libu2548/cr10core/CAD/toolhead/v1.png

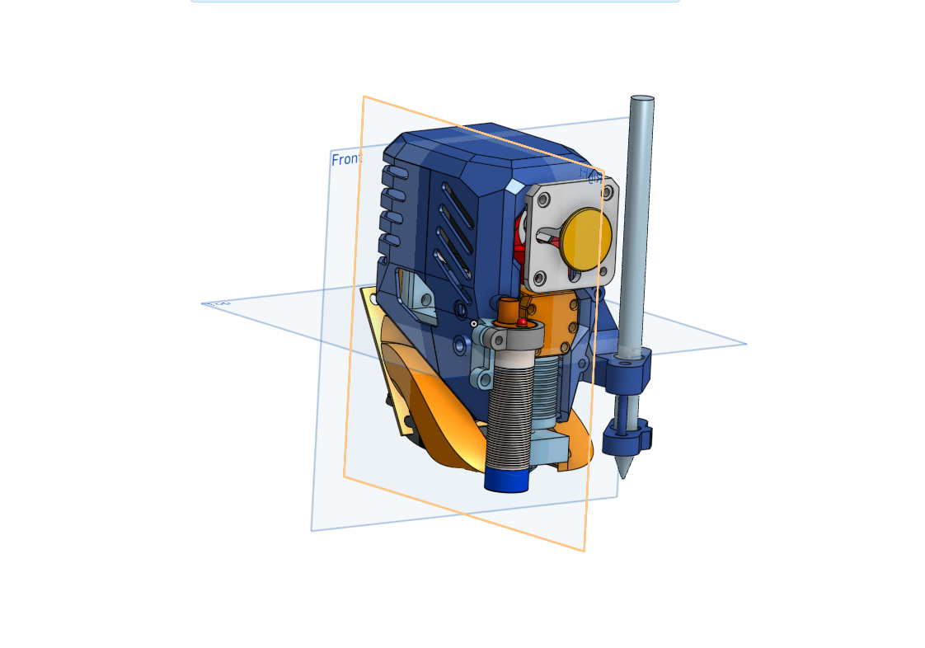
CAD/toolhead/v1.png
