libu2548/cr10core/CAD/toolhead/v3.png

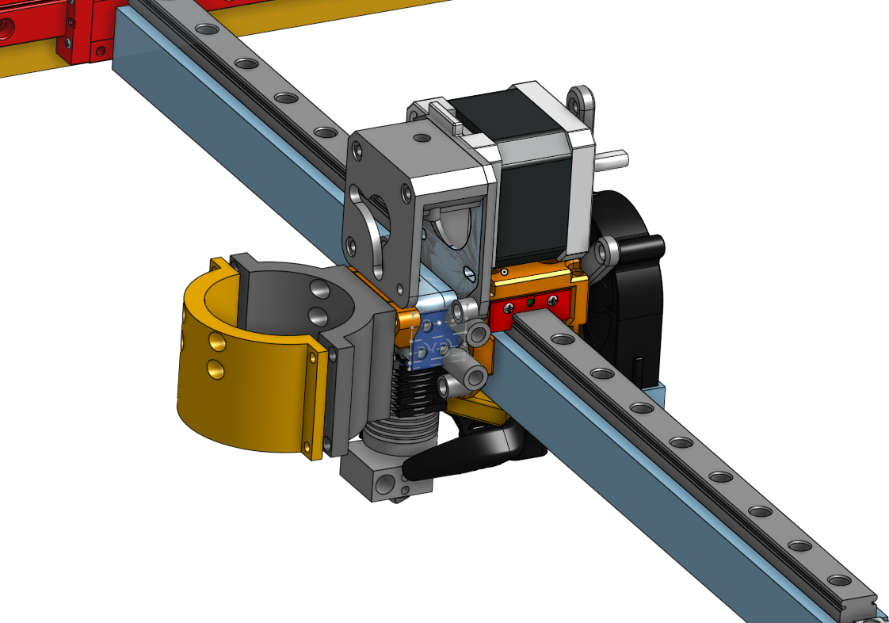
CAD/toolhead/v3.png
