libu2548/cr10core/CAD/toolhead/v4.png

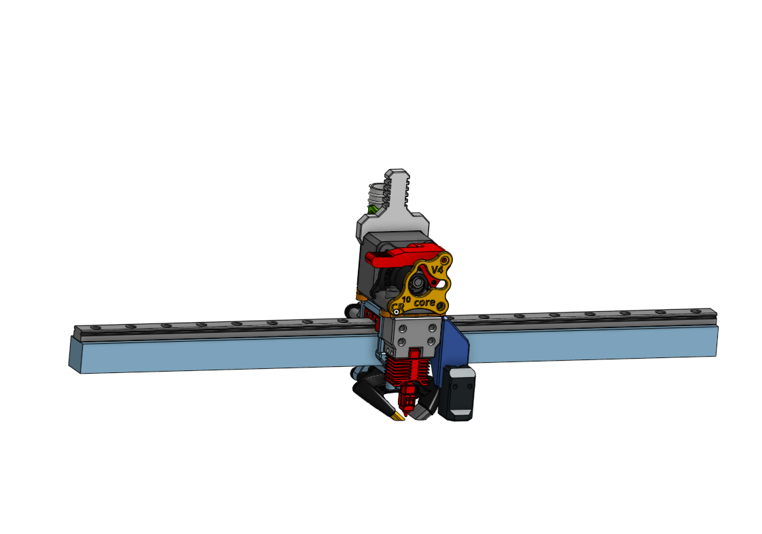
CAD/toolhead/v4.png
