libu2548/cr10core/CAD/toolhead/V5.png

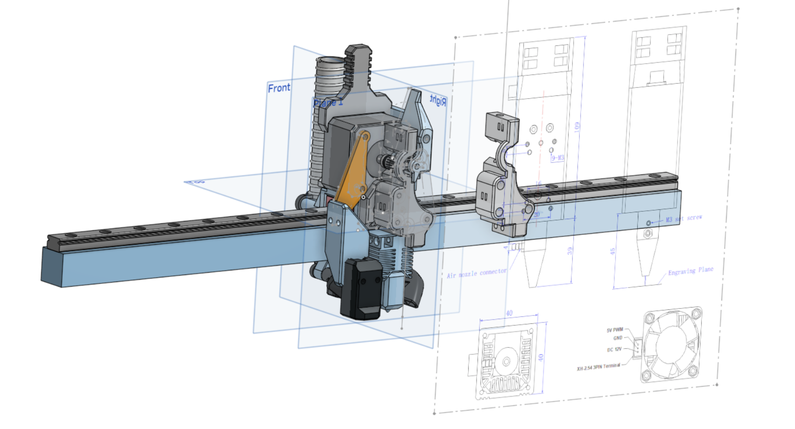
CAD/toolhead/V5.png
