libu2548/cr10core/image/20260116_104110.jpg

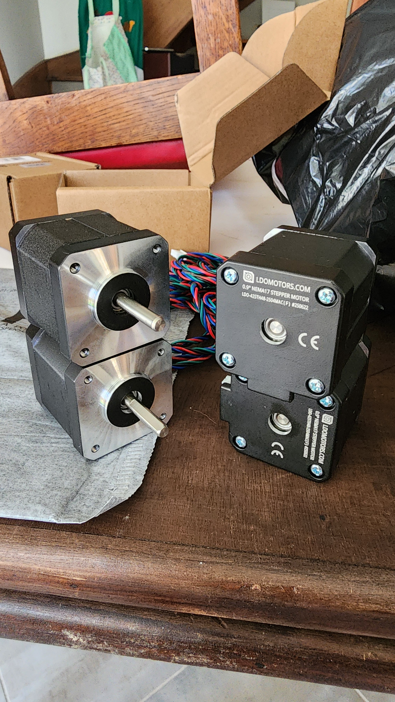
image/20260116_104110.jpg
