libu2548/cr10core/image/20260117_215310.jpg

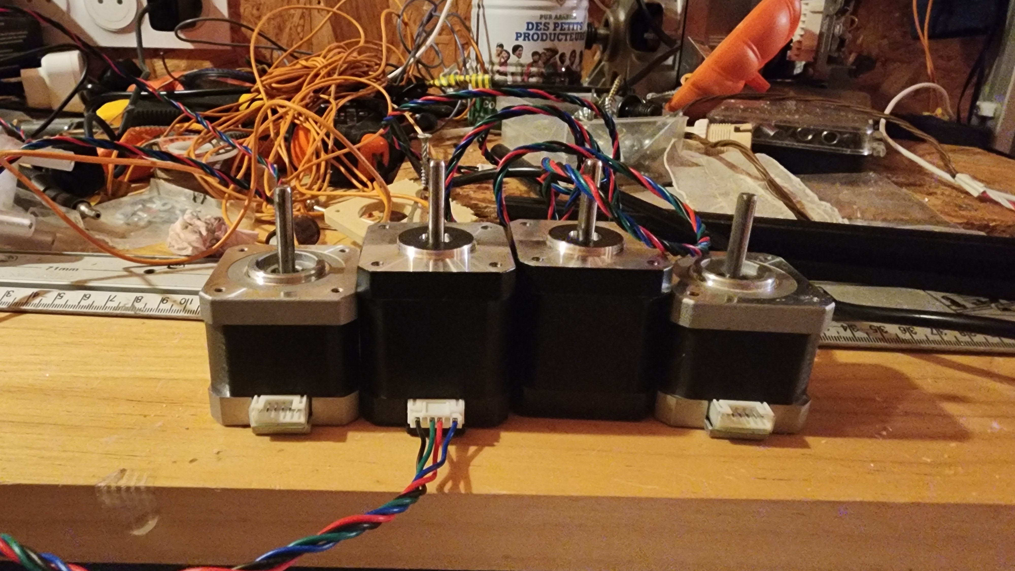
image/20260117_215310.jpg
