libu2548/cr10core/image/20260119_152943.jpg

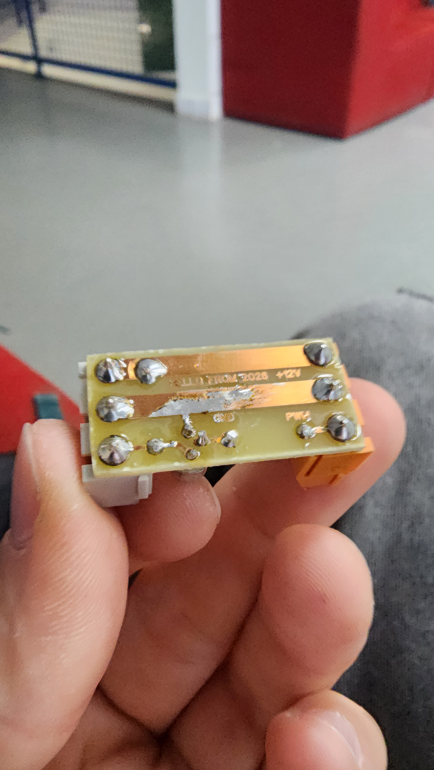
image/20260119_152943.jpg
