libu2548/cr10core/image/20260119_152947.jpg

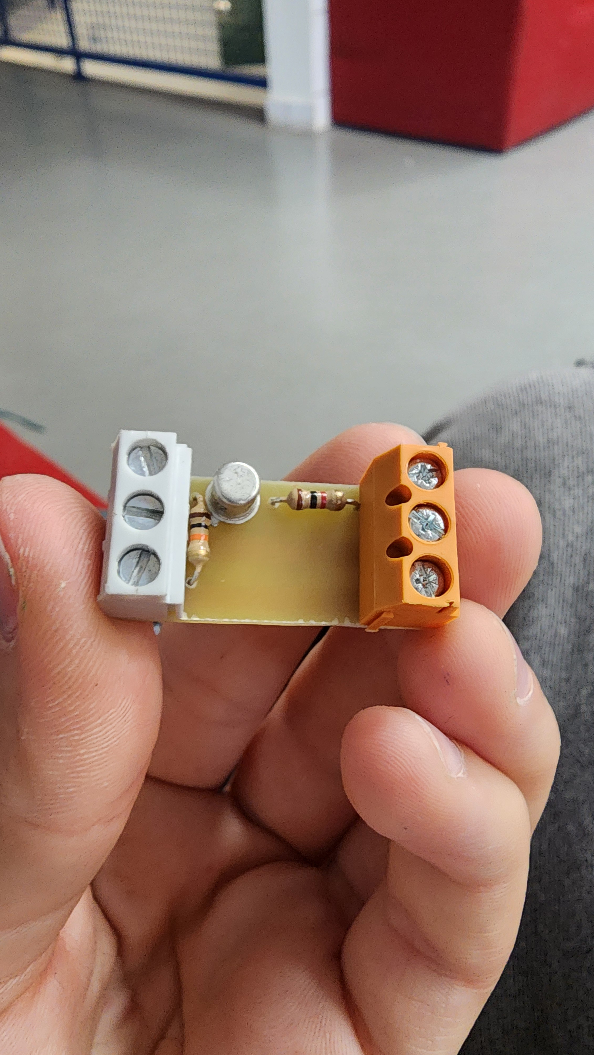
image/20260119_152947.jpg
