libu2548/cr10core/image/20260124_153731.jpg

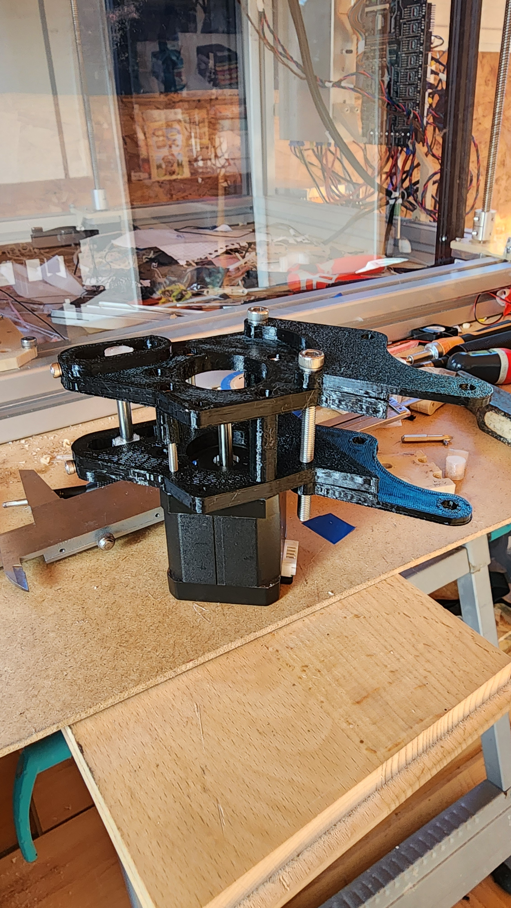
image/20260124_153731.jpg
