libu2548/cr10core/image/20260127_170606.jpg

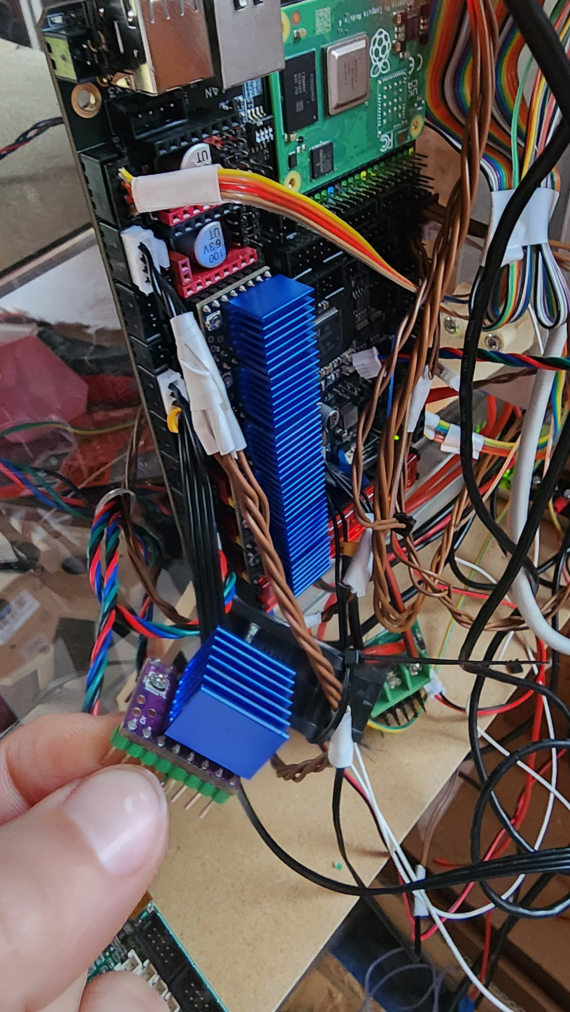
image/20260127_170606.jpg
