libu2548/cr10core/image/20260131_212745.jpg

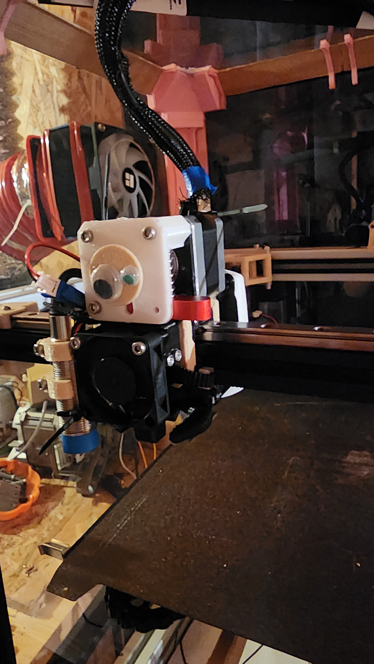
image/20260131_212745.jpg
