libu2548/cr10core/image/20260507_145341.jpg

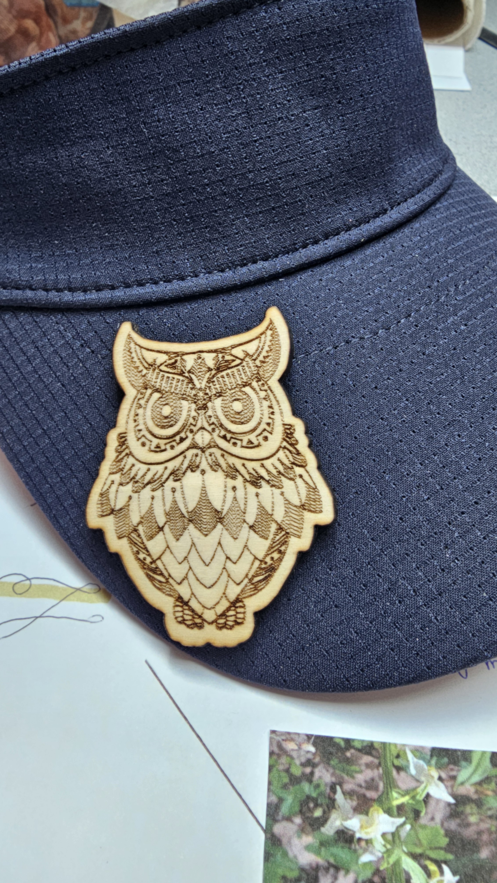
image/20260507_145341.jpg
