libu2548/cr10core/image/20260507_165830.jpg

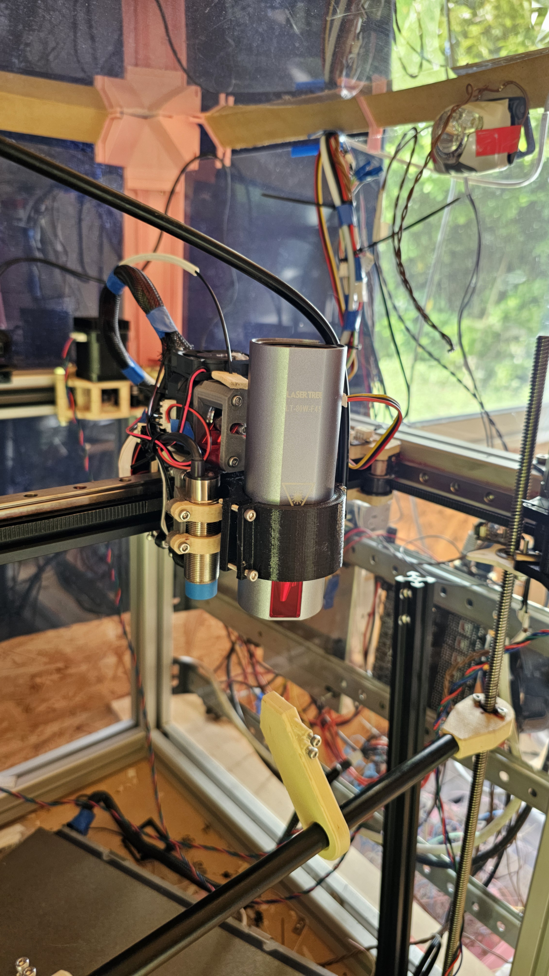
image/20260507_165830.jpg
