libu2548/cr10core/image/20260508_215619.jpg

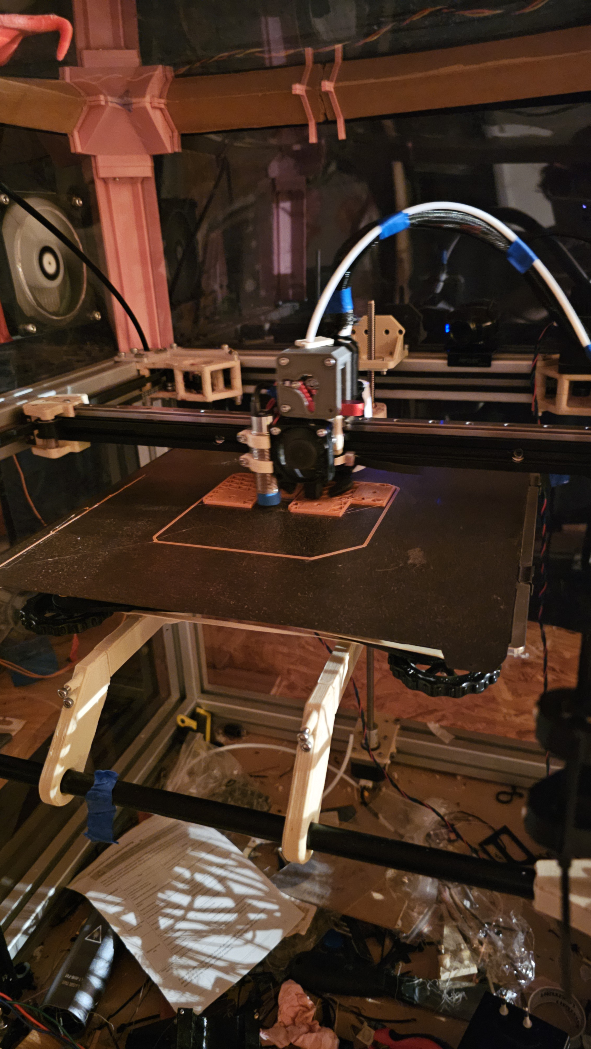
image/20260508_215619.jpg
