libu2548/cr10core/image/20260521_215504.jpg

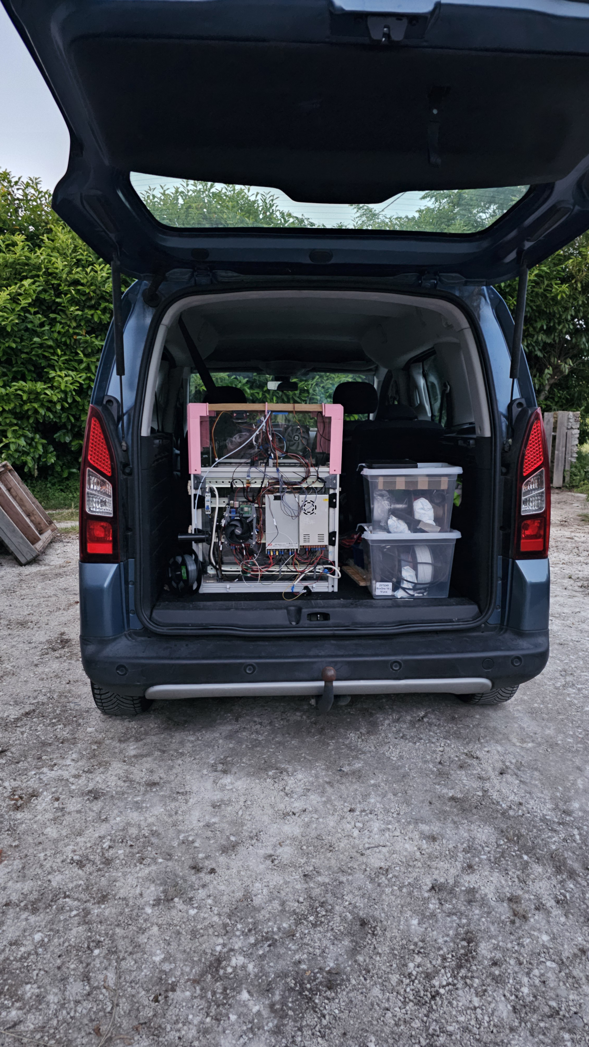
image/20260521_215504.jpg
