libu2548/cr10core/image/20260522_083416.jpg

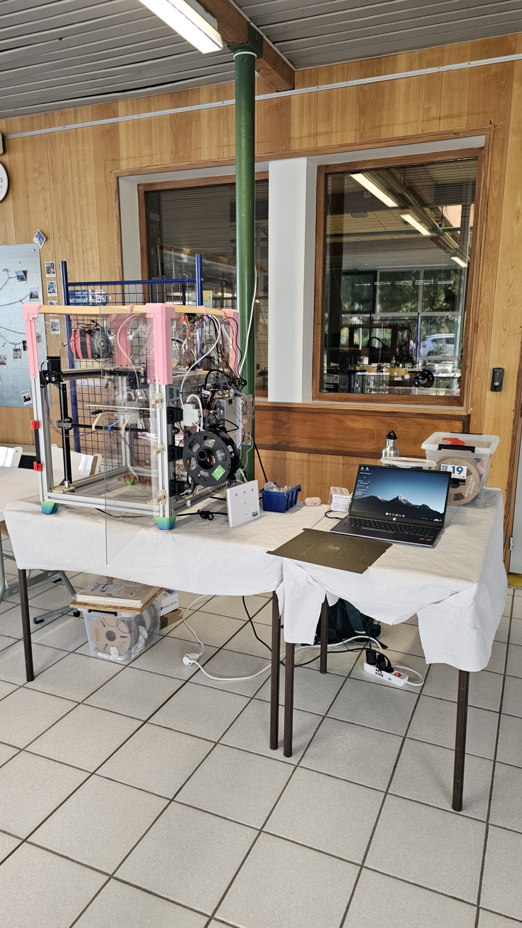
image/20260522_083416.jpg
