libu2548/cr10core/image/20260602_214717.jpg

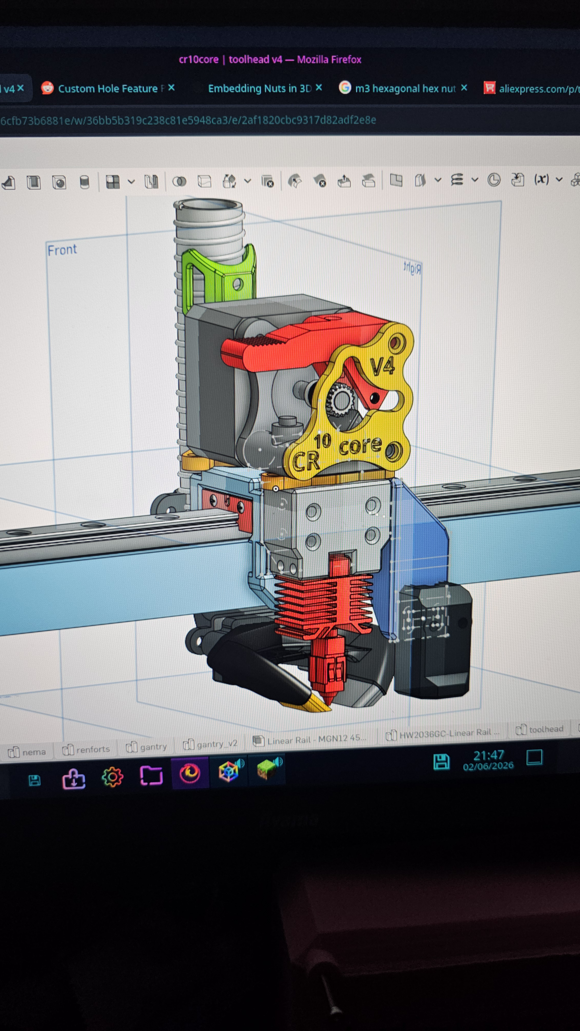
image/20260602_214717.jpg
