libu2548/cr10core/image/20260611_225606.jpg

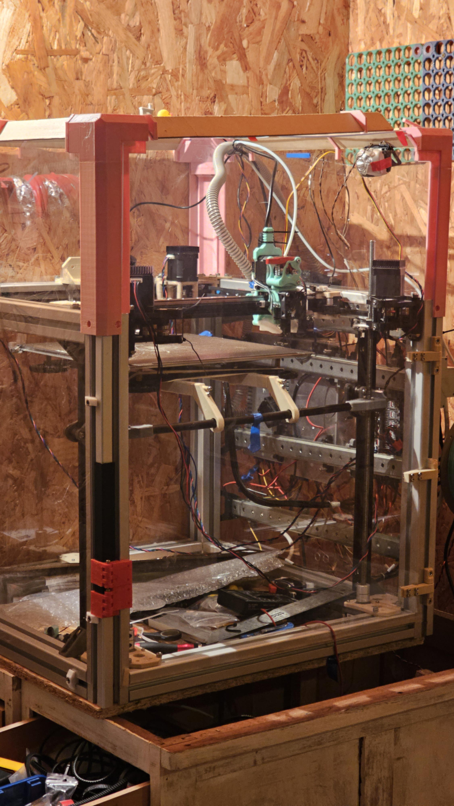
image/20260611_225606.jpg
