libu2548/cr10core/image/20260623_185925.jpg

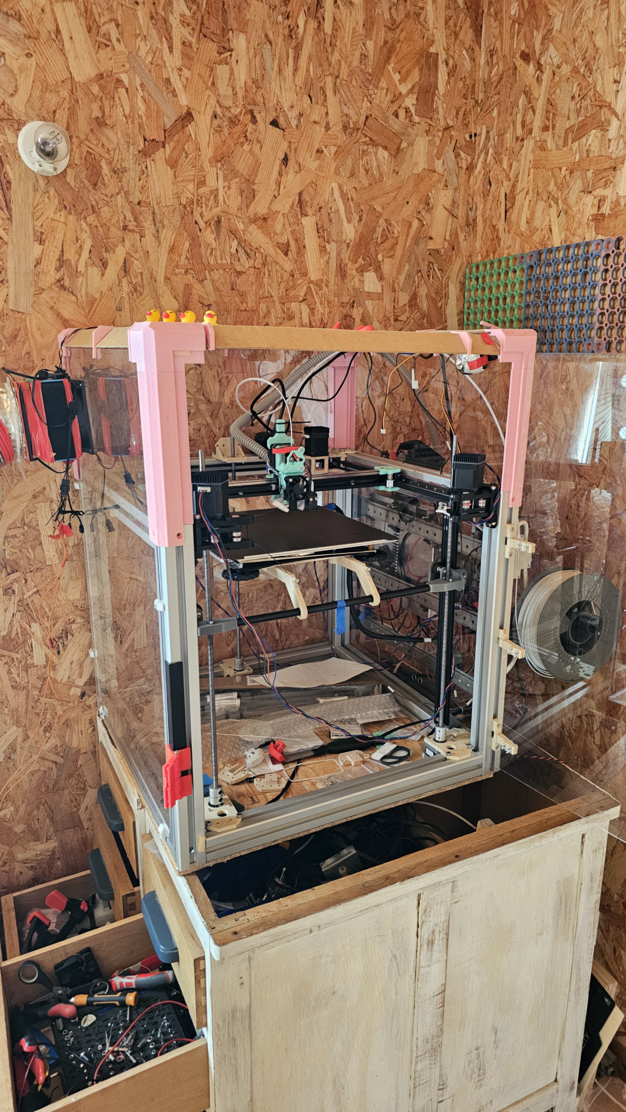
image/20260623_185925.jpg
