libu2548/cr10core/image/20260626_155403.jpg

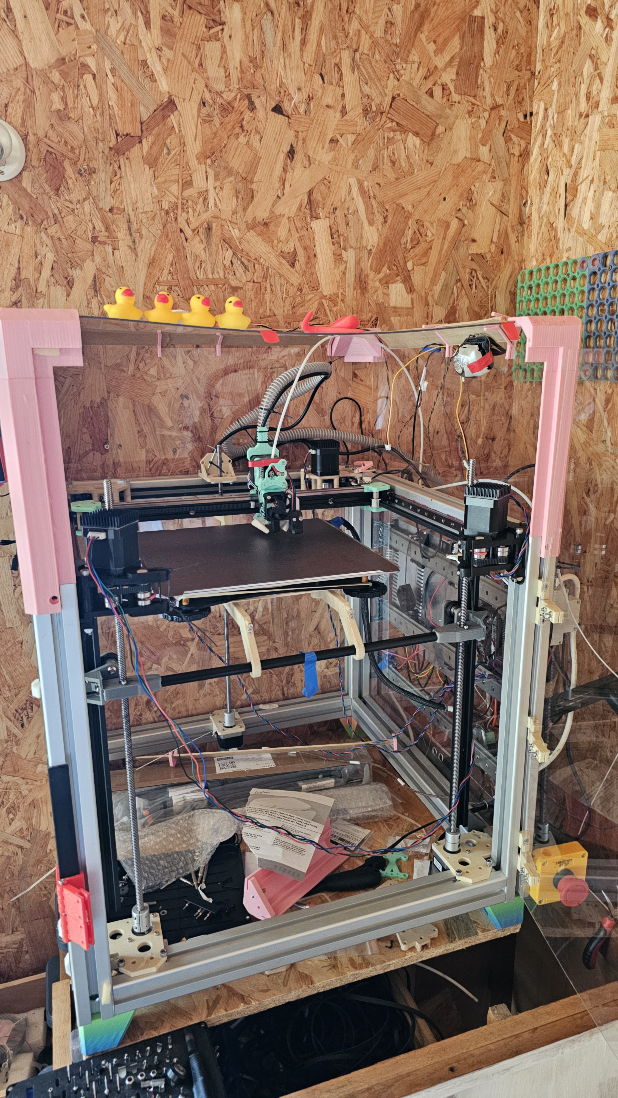
image/20260626_155403.jpg
