libu2548/cr10core/image/20260629_121632.jpg

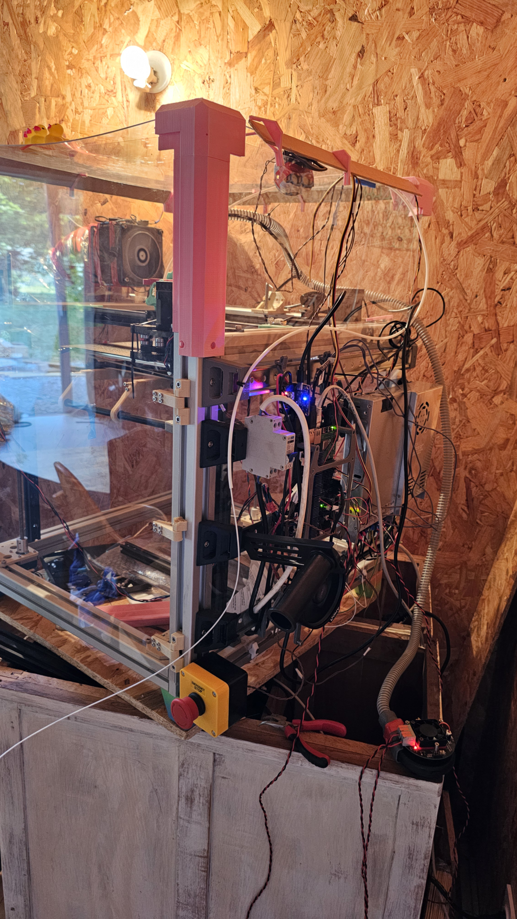
image/20260629_121632.jpg
