libu2548/cr10core/image/20260630_170940.jpg

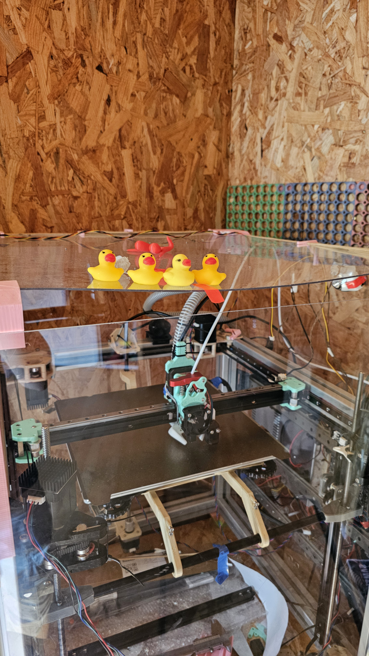
image/20260630_170940.jpg
