libu2548/cr10core/image/20260810_182935.jpg

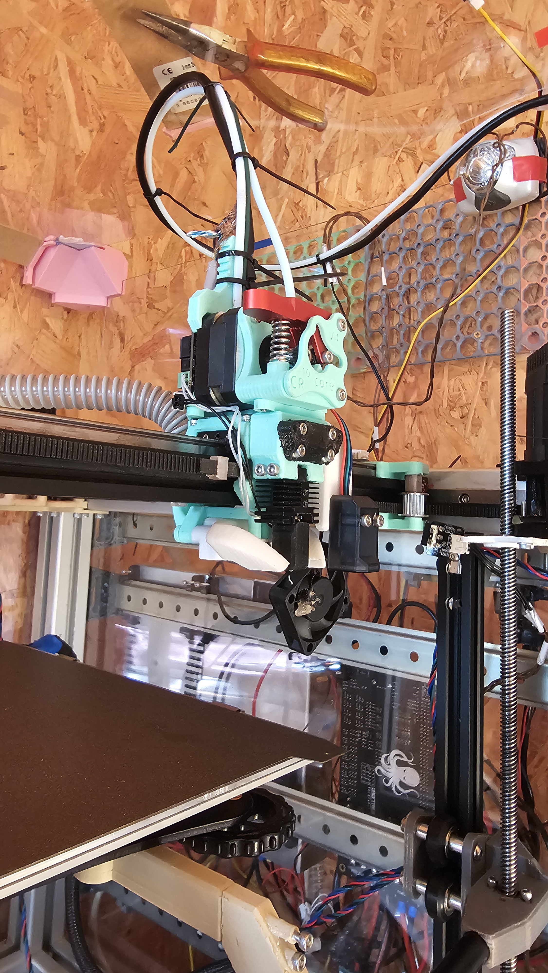
image/20260810_182935.jpg
