libu2548/cr10core/image/20260810_183454.jpg

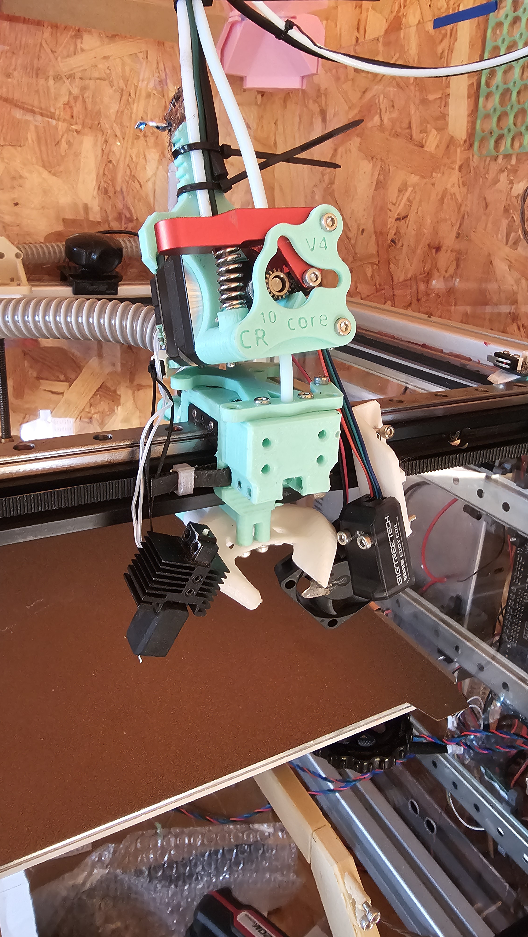
image/20260810_183454.jpg
