libu2548/cr10core/image/20260810_183547.jpg

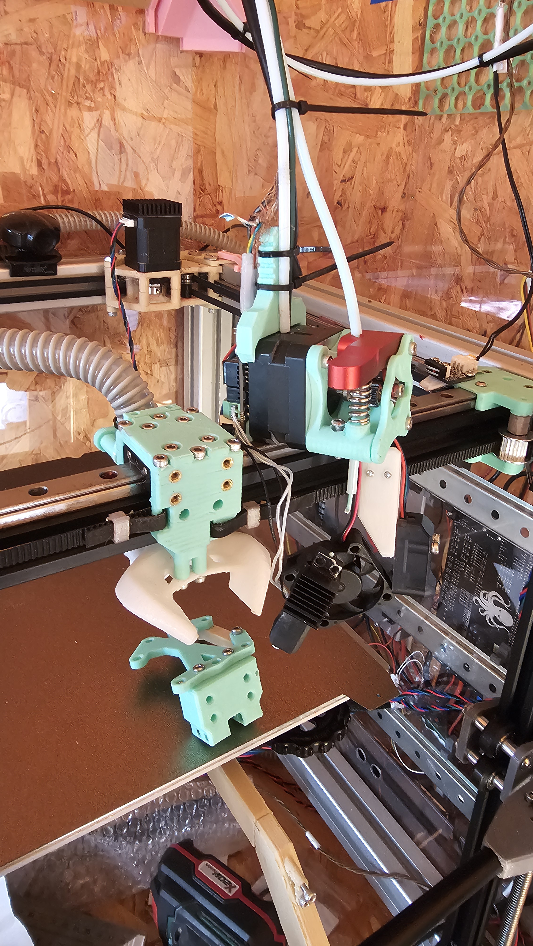
image/20260810_183547.jpg
