libu2548/cr10core/image/20260810_230010.jpg

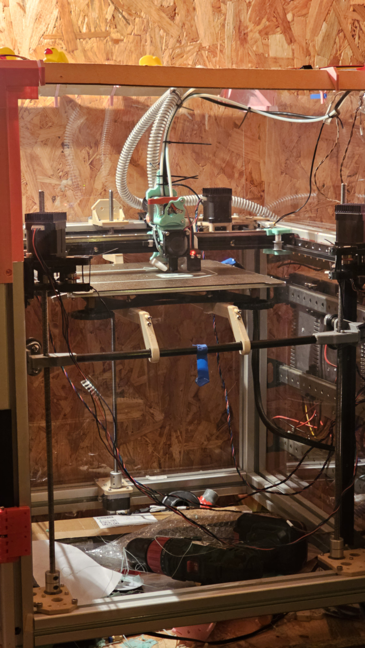
image/20260810_230010.jpg
