libu2548/cr10core/image/20260913_220324.jpg

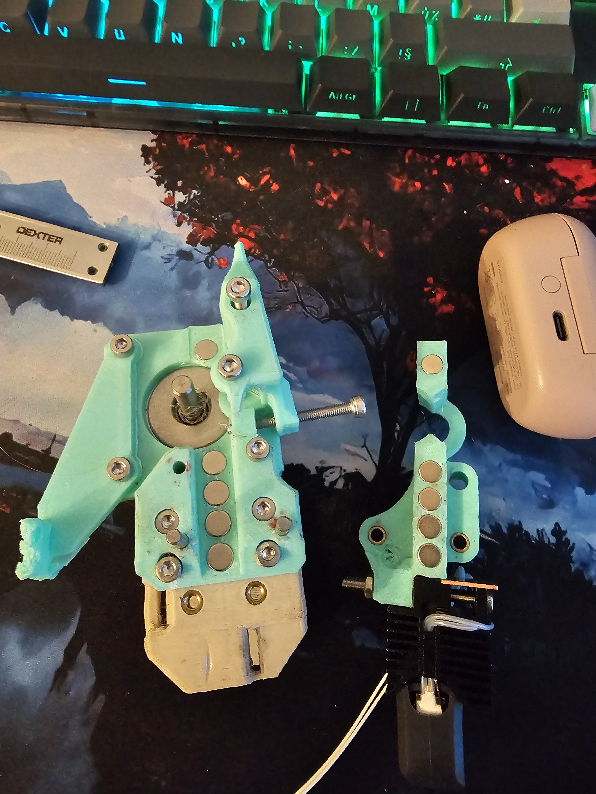
image/20260913_220324.jpg
