libu2548/cr10core/CAD/toolhead/toolhead v4 indiv files/toolhead v4 - Open CASCADE STEP translator 6.8 1.1.1.step

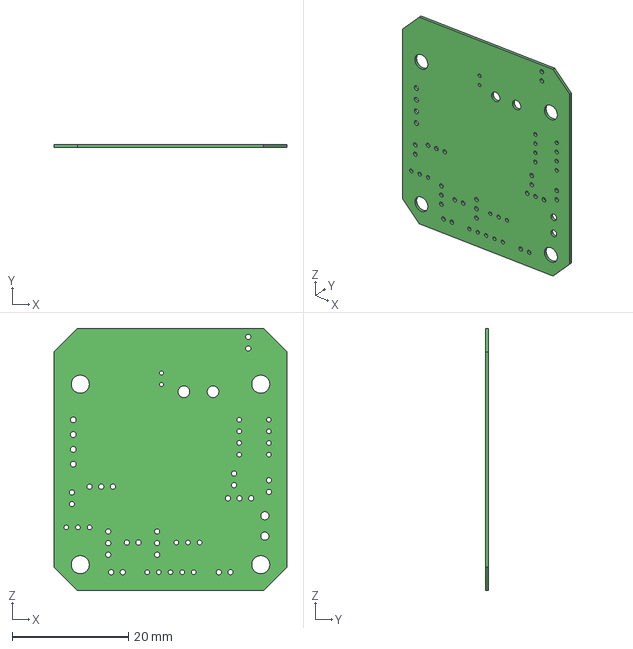
[picture p53: CAD file, 2026-08-19]
CAD/toolhead/toolhead v4 indiv files/toolhead v4 - Open CASCADE STEP translator 6.8 1.1.1.step
40.0 x 0.558 x 45.0 mm
