libu2548/cr10core/CAD/toolhead/toolhead v4 indiv files/toolhead v4 - MGN12C Carriage v1.step

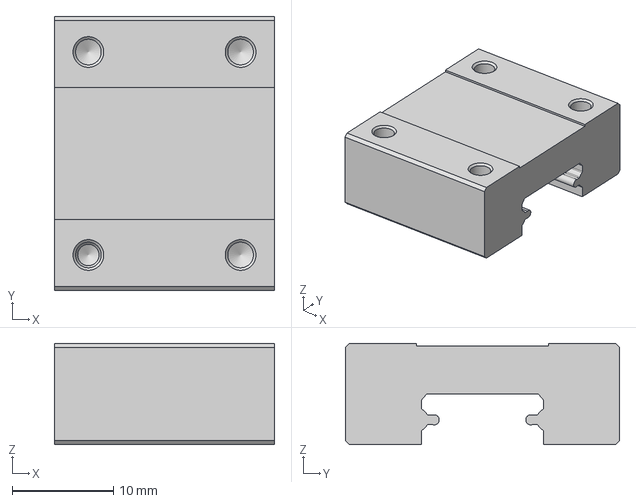
[picture p54: CAD file, 2026-08-19]
CAD/toolhead/toolhead v4 indiv files/toolhead v4 - MGN12C Carriage v1.step
21.7 x 27.0 x 10.0 mm
