libu2548/cr10core/CAD/toolhead/toolhead v4 indiv files/toolhead v4 - Part 22.step

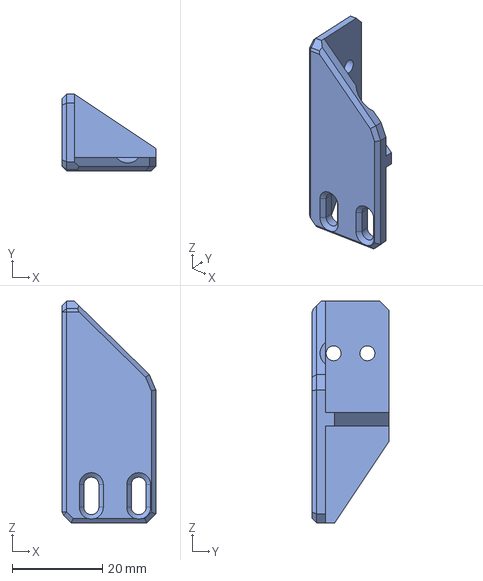
[picture p55: CAD file, 2026-08-19]
CAD/toolhead/toolhead v4 indiv files/toolhead v4 - Part 22.step
20.8 x 17.0 x 49.2 mm
