libu2548/cr10core/CAD/toolhead/toolhead v4 indiv files/toolhead v4 - CPAP clamp.step

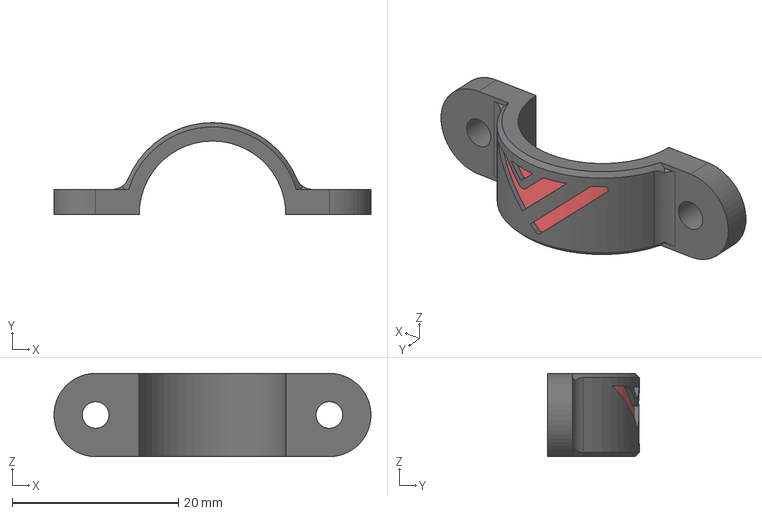
[picture p56: CAD file, 2026-08-19]
CAD/toolhead/toolhead v4 indiv files/toolhead v4 - CPAP clamp.step
38.1 x 11.0 x 10.0 mm
