libu2548/cr10core/CAD/toolhead/toolhead v4 indiv files/toolhead v4 - Motor gear.step

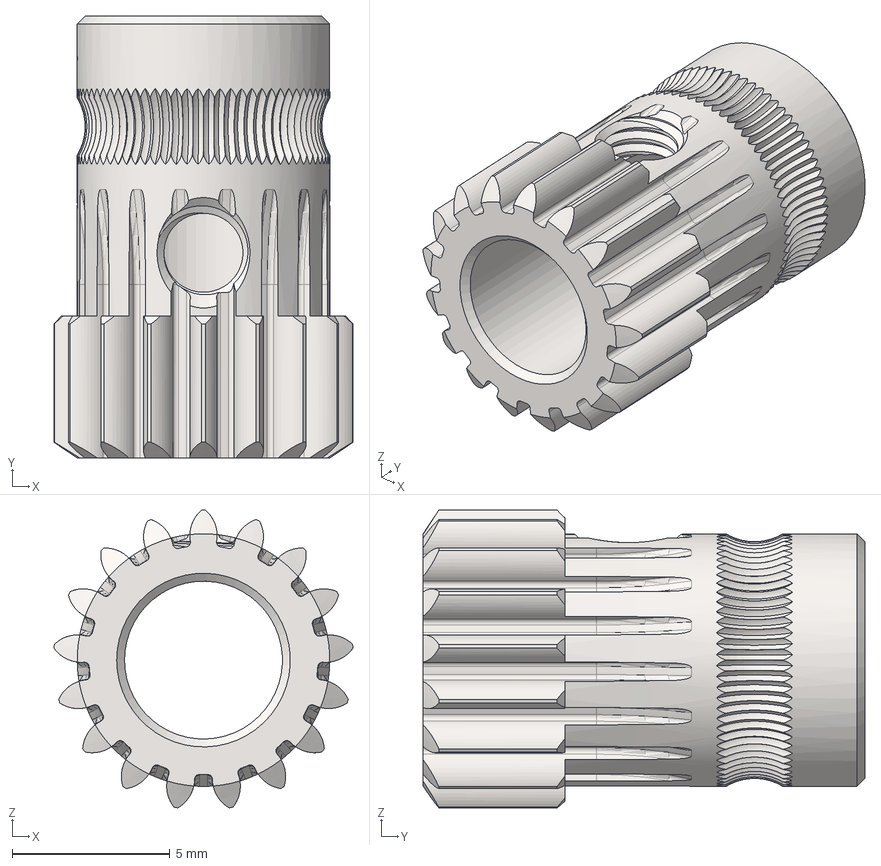
[picture p57: CAD file, 2026-08-19]
CAD/toolhead/toolhead v4 indiv files/toolhead v4 - Motor gear.step
9.47 x 14.0 x 9.43 mm
