libu2548/cr10core/CAD/toolhead/toolhead v4 indiv files/toolhead v4 - Part 31.step

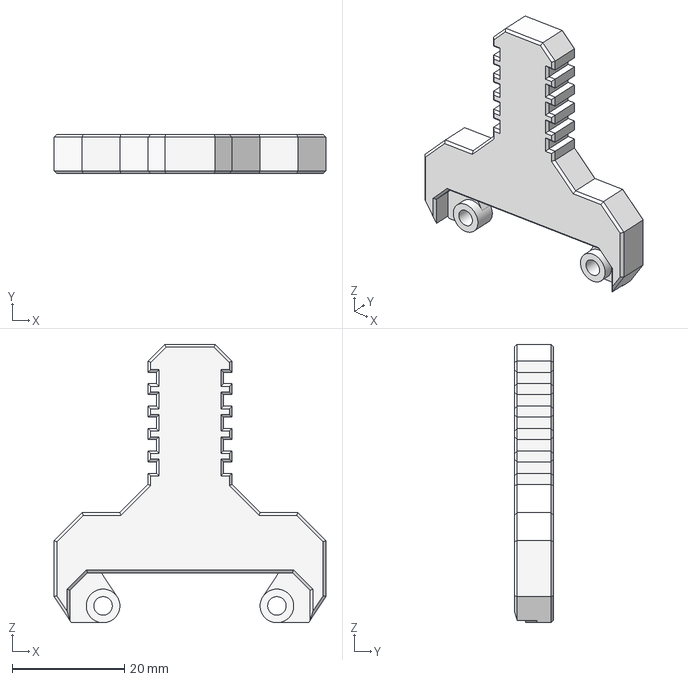
[picture p58: CAD file, 2026-08-19]
CAD/toolhead/toolhead v4 indiv files/toolhead v4 - Part 31.step
48.5 x 7.00 x 49.6 mm
