libu2548/cr10core/CAD/toolhead/toolhead v4 indiv files/toolhead v4 - chassis.step

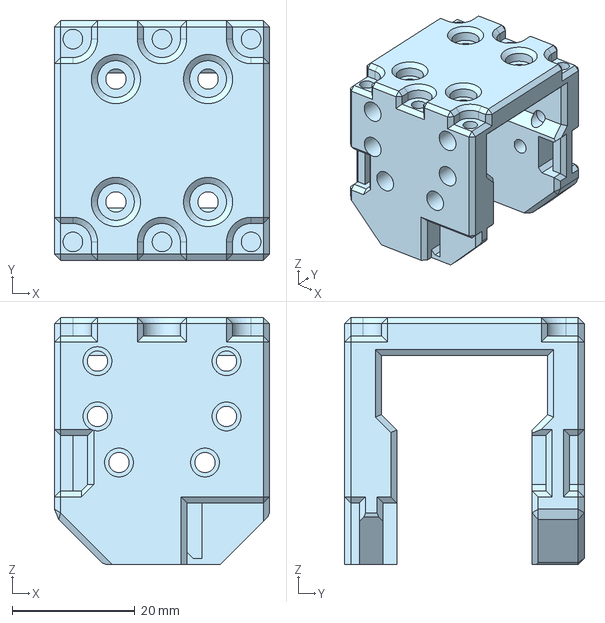
[picture p59: CAD file, 2026-08-19]
CAD/toolhead/toolhead v4 indiv files/toolhead v4 - chassis.step
35.0 x 39.0 x 40.2 mm
