libu2548/cr10core/CAD/toolhead/toolhead v4 indiv files/toolhead v4 - extrudeur.step

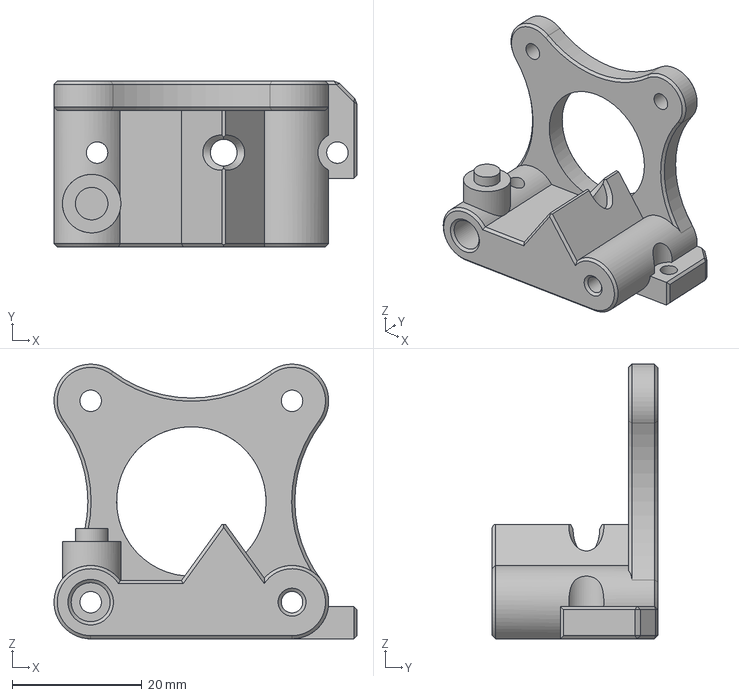
[picture p60: CAD file, 2026-08-19]
CAD/toolhead/toolhead v4 indiv files/toolhead v4 - extrudeur.step
46.6 x 25.5 x 42.3 mm
