libu2548/cr10core/CAD/toolhead/toolhead v4 indiv files/toolhead v4 - cable holder Vz (1).step

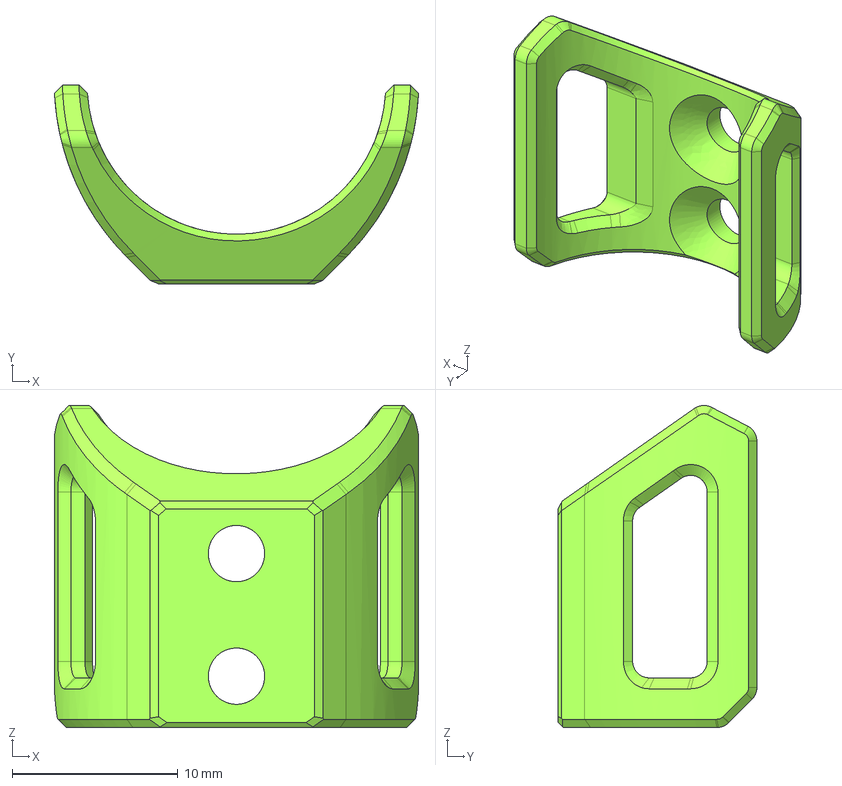
[picture p61: CAD file, 2026-08-19]
CAD/toolhead/toolhead v4 indiv files/toolhead v4 - cable holder Vz (1).step
22.0 x 12.0 x 19.4 mm
