libu2548/cr10core/CAD/toolhead/toolhead v4 indiv files/toolhead v4 - Part 29.step

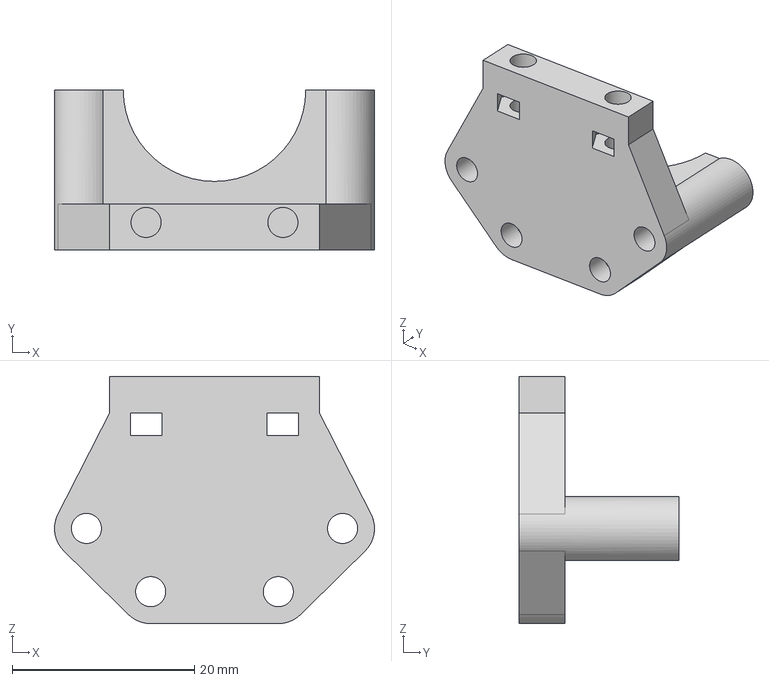
[picture p62: CAD file, 2026-08-19]
CAD/toolhead/toolhead v4 indiv files/toolhead v4 - Part 29.step
35.1 x 17.5 x 27.1 mm
