libu2548/cr10core/CAD/toolhead/toolhead v4 indiv files/toolhead v4 - Hotend.step

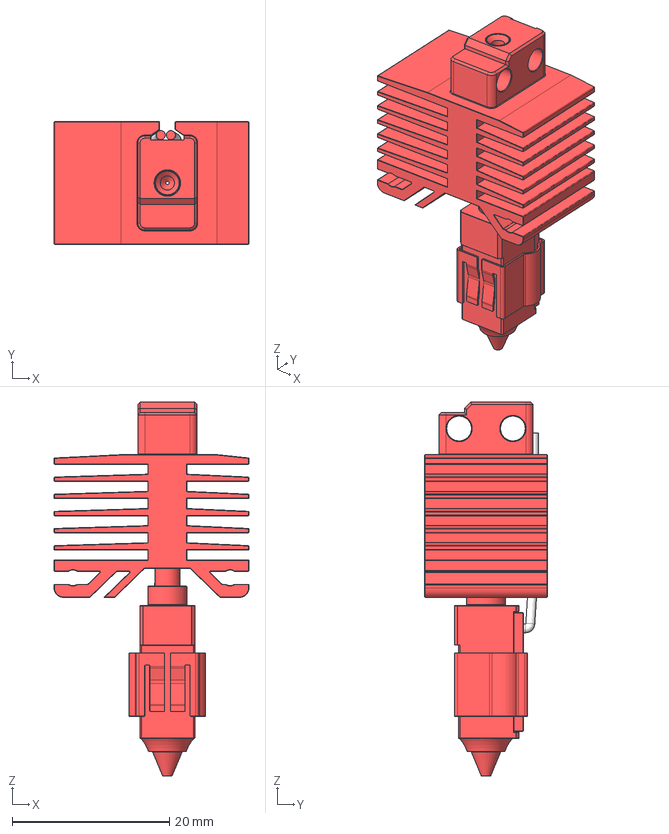
[picture p63: CAD file, 2026-08-19]
CAD/toolhead/toolhead v4 indiv files/toolhead v4 - Hotend.step
24.8 x 15.6 x 47.6 mm
