libu2548/cr10core/CAD/toolhead/toolhead v4 indiv files/toolhead v4 - cpap tube.step

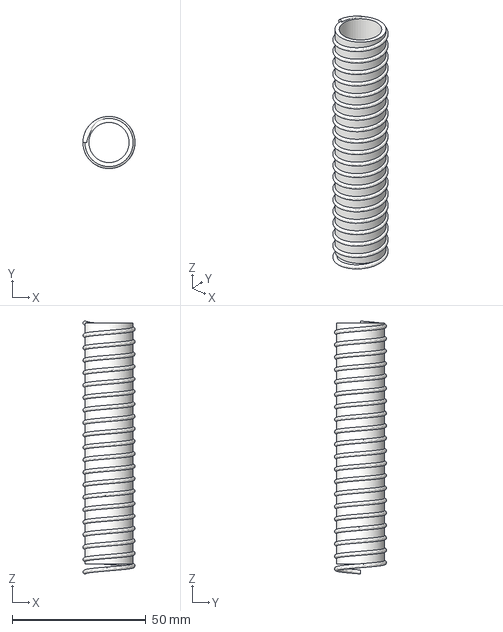
[picture p64: CAD file, 2026-08-19]
CAD/toolhead/toolhead v4 indiv files/toolhead v4 - cpap tube.step
19.5 x 19.5 x 94.5 mm
