libu2548/cr10core/CAD/toolhead/toolhead v4 indiv files/toolhead v4 - hotend bloc.step

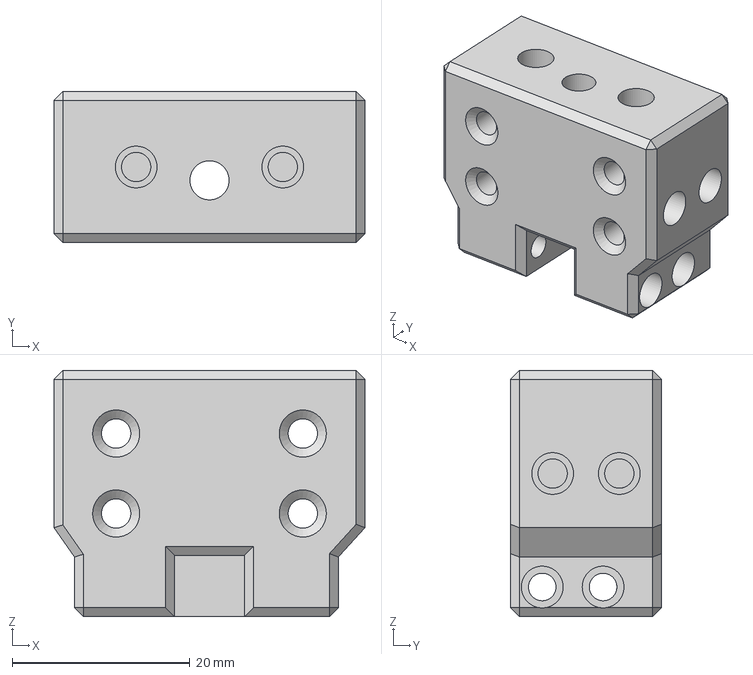
[picture p65: CAD file, 2026-08-19]
CAD/toolhead/toolhead v4 indiv files/toolhead v4 - hotend bloc.step
35.0 x 17.0 x 27.7 mm
