libu2548/cr10core/CAD/toolhead/toolhead v4 indiv files/toolhead v4 - Linear Rail - MGN12 450mm + MGN12C carriage v1.step

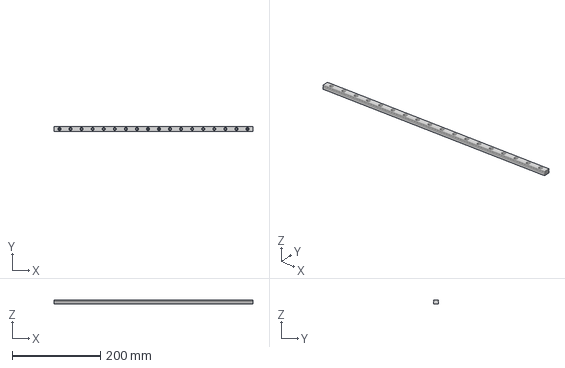
[picture p66: CAD file, 2026-08-19]
CAD/toolhead/toolhead v4 indiv files/toolhead v4 - Linear Rail - MGN12 450mm + MGN12C carriage v1.step
450.0 x 12.0 x 8.00 mm
