libu2548/cr10core/CAD/toolhead/toolhead v4 indiv files/toolhead v4 - Goliath short Beacon.step

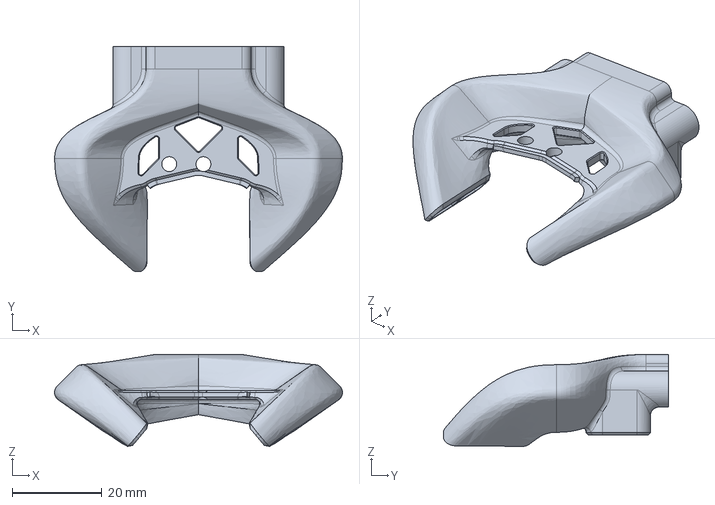
[picture p67: CAD file, 2026-08-19]
CAD/toolhead/toolhead v4 indiv files/toolhead v4 - Goliath short Beacon.step
64.0 x 50.1 x 20.5 mm
