libu2548/cr10core/CAD/toolhead/toolhead v4 indiv files/toolhead v4 - Nema 17 Slim.step

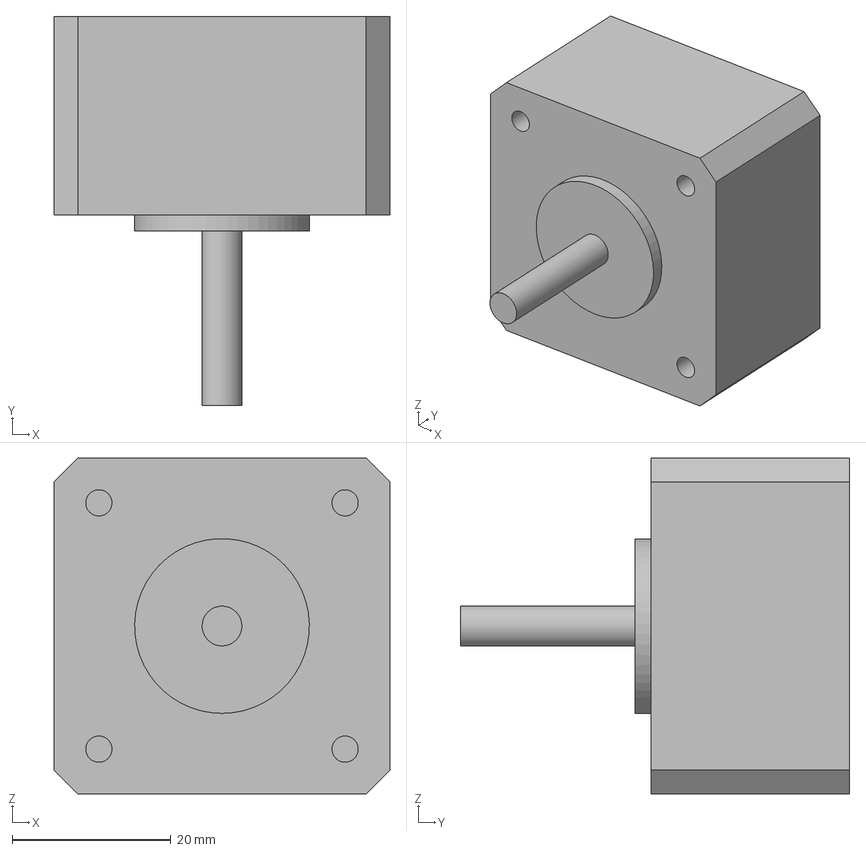
[picture p68: CAD file, 2026-08-19]
CAD/toolhead/toolhead v4 indiv files/toolhead v4 - Nema 17 Slim.step
42.3 x 49.0 x 42.3 mm
