libu2548/cr10core/CAD/toolhead/toolhead v4 indiv files/toolhead v4 - BTT Eddy Coil.step

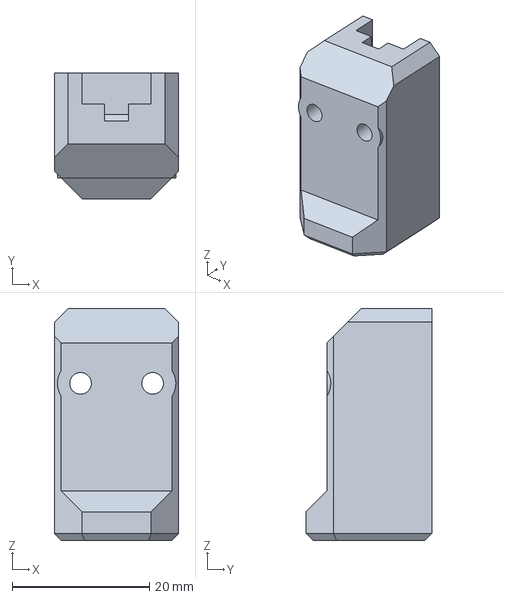
[picture p69: CAD file, 2026-08-19]
CAD/toolhead/toolhead v4 indiv files/toolhead v4 - BTT Eddy Coil.step
18.1 x 18.3 x 33.8 mm
