libu2548/cr10core/CAD/toolhead/toolhead v4 indiv files/toolhead v4 - NAMEIMPRIMANTE.step

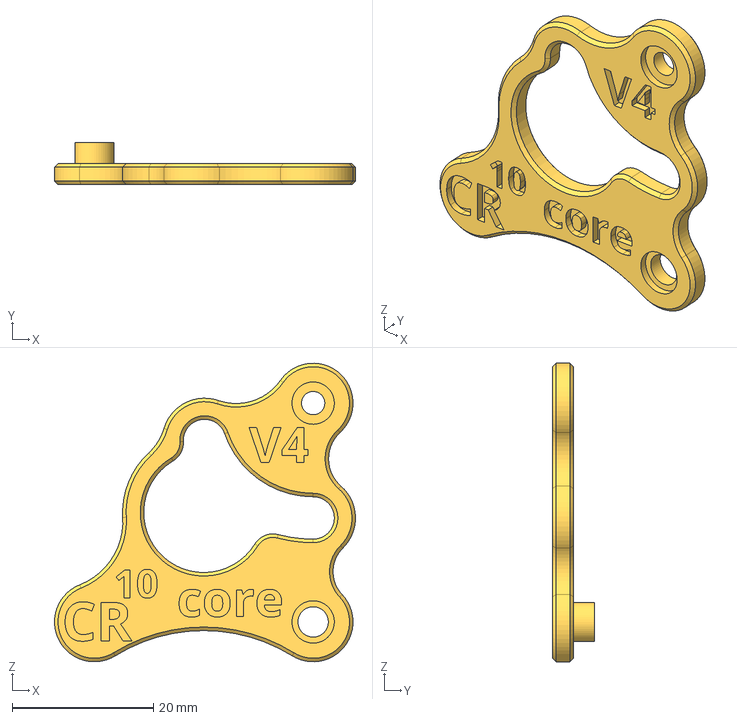
[picture p70: CAD file, 2026-08-19]
CAD/toolhead/toolhead v4 indiv files/toolhead v4 - NAMEIMPRIMANTE.step
42.6 x 6.00 x 42.3 mm
