libu2548/cr10core/CAD/toolhead/toolhead v4 indiv files/toolhead v4 - Part 7.step

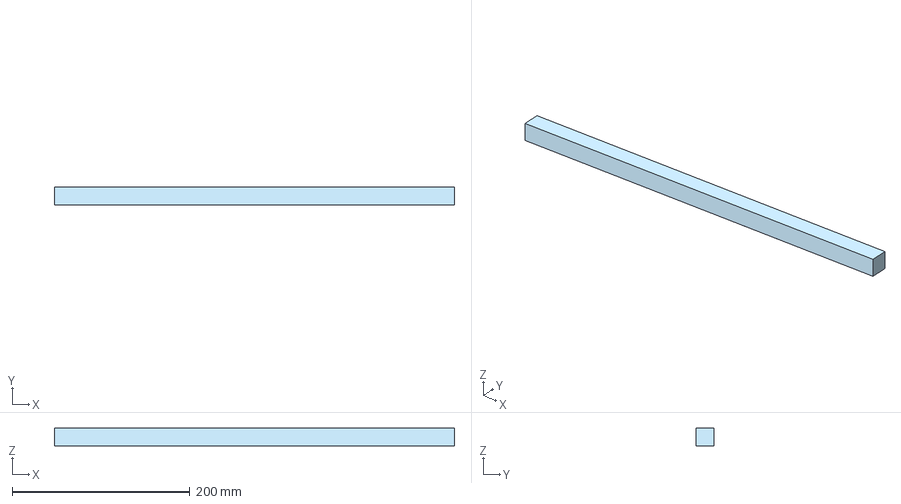
[picture p71: CAD file, 2026-08-19]
CAD/toolhead/toolhead v4 indiv files/toolhead v4 - Part 7.step
450.0 x 20.0 x 20.0 mm
