libu2548/cr10core/CAD/toolhead/toolhead v4 indiv files/toolhead v4 - bracket.step

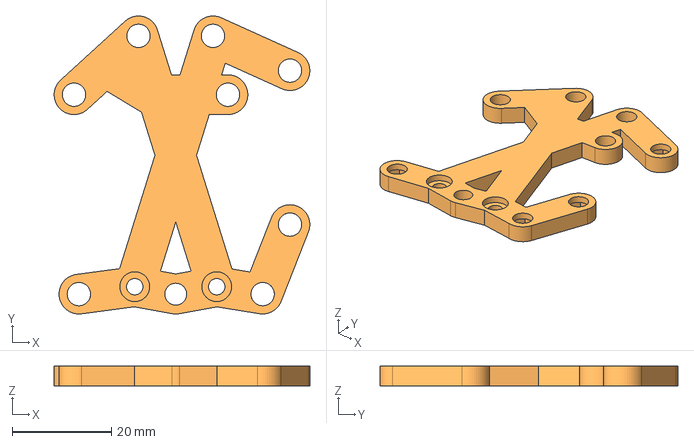
[picture p72: CAD file, 2026-08-19]
CAD/toolhead/toolhead v4 indiv files/toolhead v4 - bracket.step
51.5 x 60.0 x 4.00 mm
