libu2548/cr10core/CAD/toolhead/toolhead v4 indiv files/toolhead v4 - Part 32.step

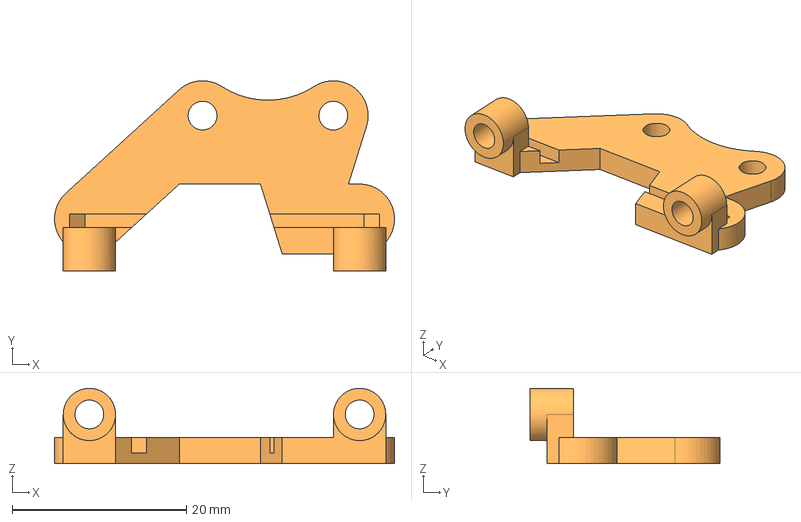
[picture p73: CAD file, 2026-08-19]
CAD/toolhead/toolhead v4 indiv files/toolhead v4 - Part 32.step
39.0 x 21.8 x 8.65 mm
