libu2548/cr10core/CAD/toolhead/toolhead v4 indiv files/toolhead v4 - housing.step

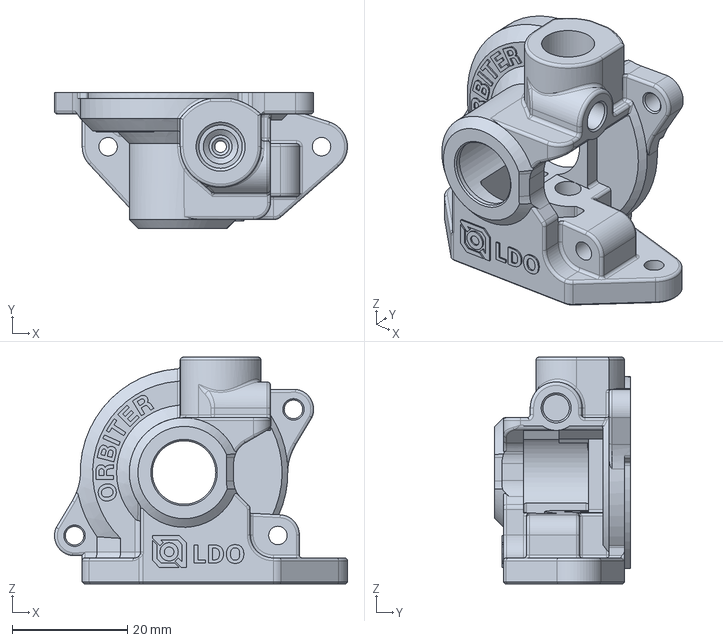
[picture p74: CAD file, 2026-08-19]
CAD/toolhead/toolhead v4 indiv files/toolhead v4 - housing.step
50.8 x 23.5 x 39.3 mm
