libu2548/cr10core/image/20260115_185155.jpg

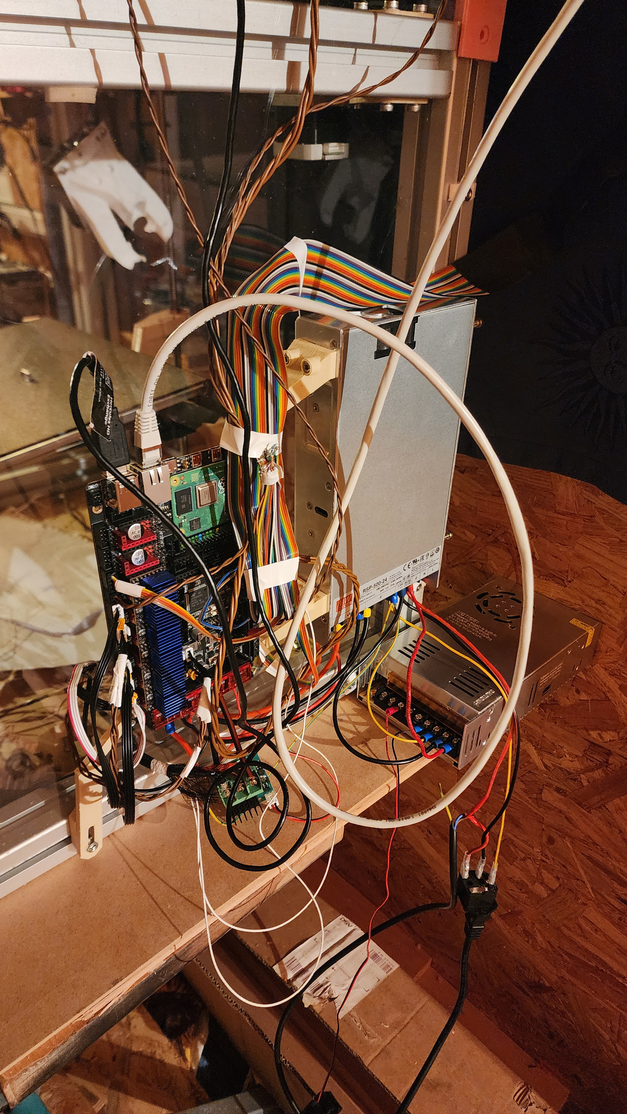
image/20260115_185155.jpg
