libu2548/cr10core/image/20260115_202628.jpg

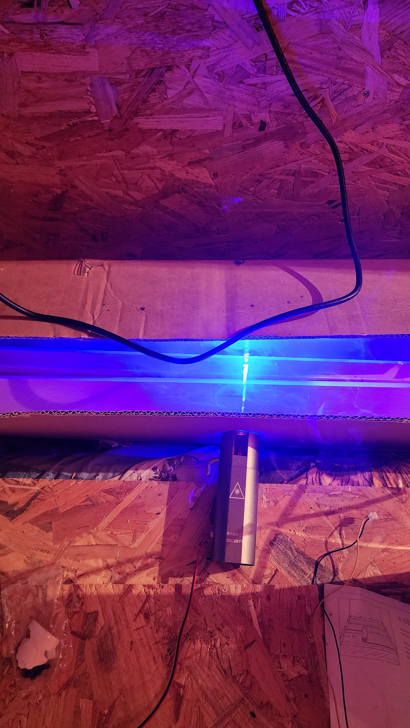
image/20260115_202628.jpg
