libu2548/cr10core/image/20260131_193423.jpg

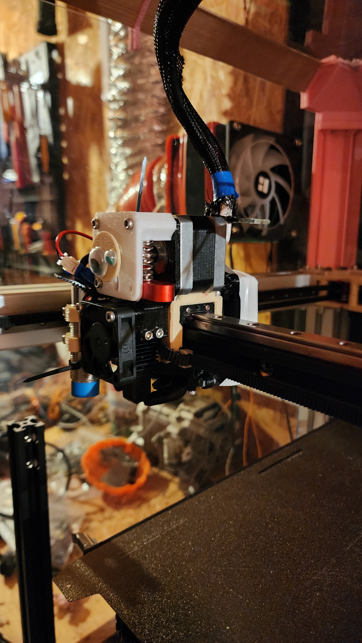
image/20260131_193423.jpg
