libu2548/cr10core/image/20260131_212953.jpg

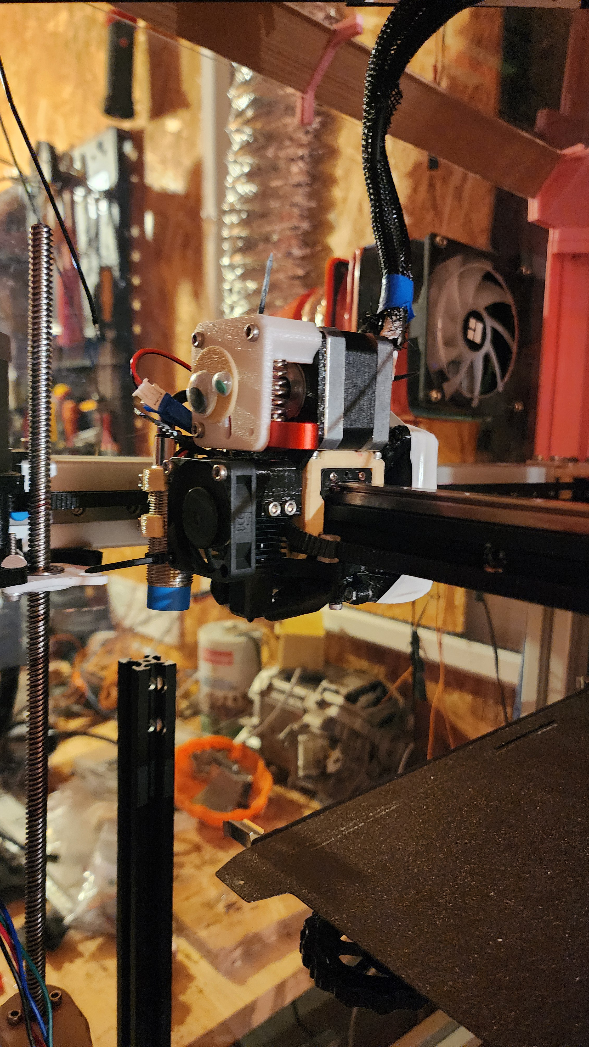
image/20260131_212953.jpg
