libu2548/cr10core/image/20260910_222637.jpg

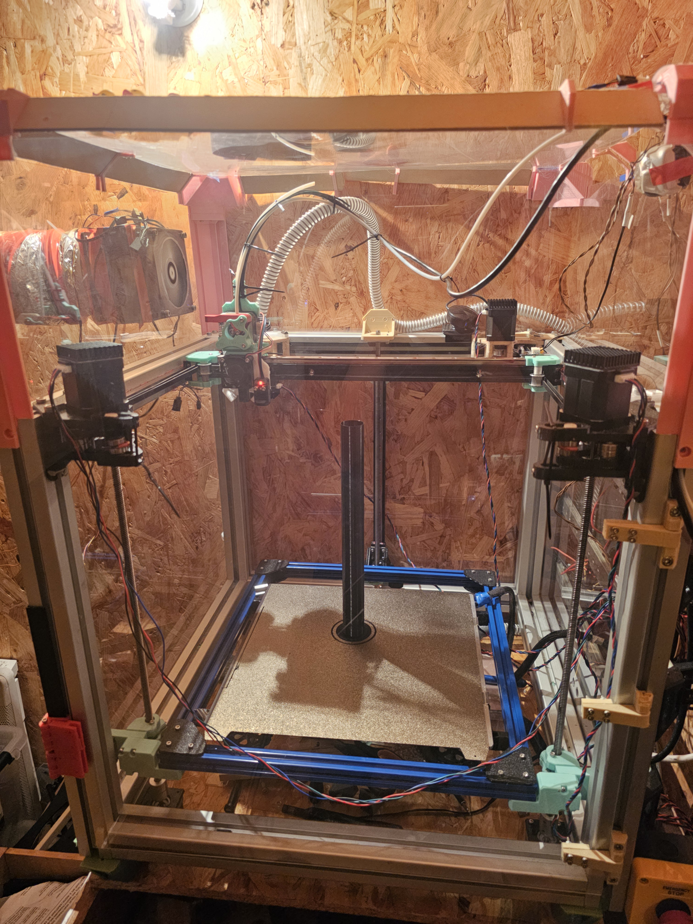
image/20260910_222637.jpg
